Rex-Josaphat/MechaCrypt-Portfolio/assets/images/AES/aesCoreTB.png

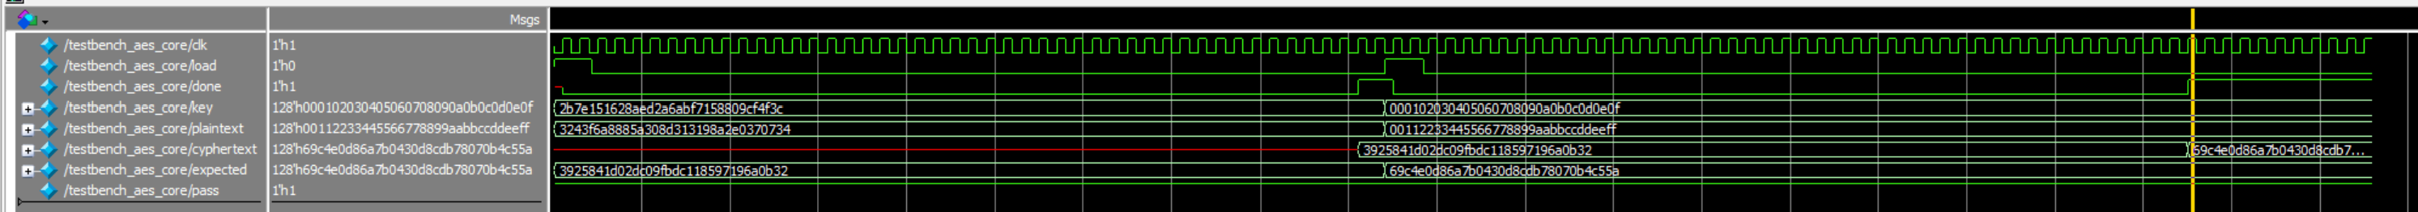
assets/images/AES/aesCoreTB.png
