Rex-Josaphat/MechaCrypt-Portfolio/assets/images/AES/getNextKeyTB.png

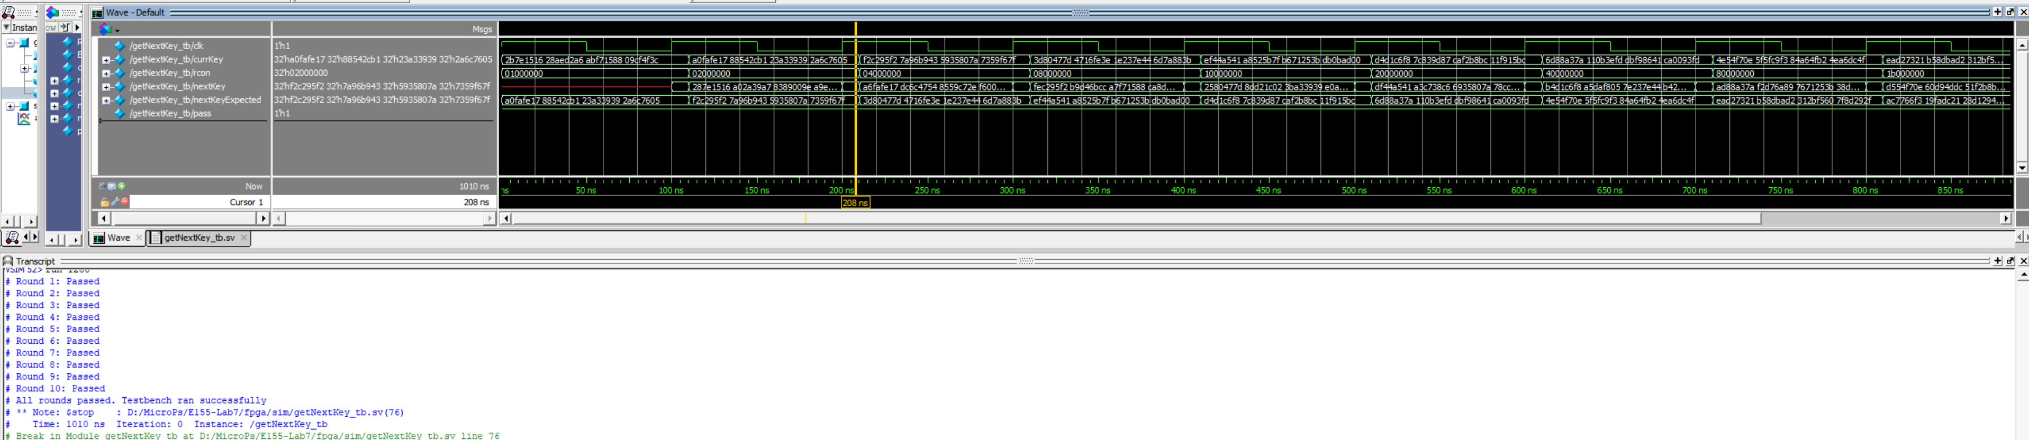
assets/images/AES/getNextKeyTB.png
