Rex-Josaphat/MechaCrypt-Portfolio/assets/images/AES/subBytesTB.png

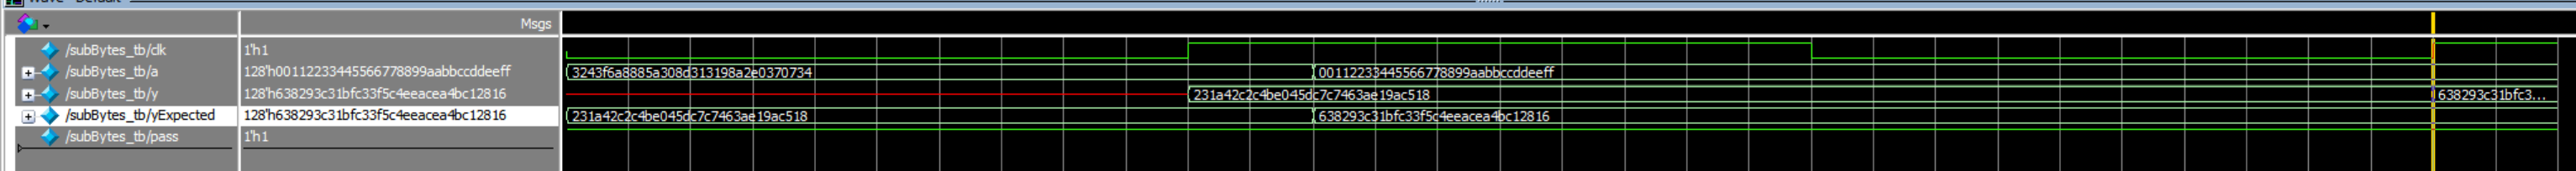
assets/images/AES/subBytesTB.png
